dretay/stm32l051c8t_pulsar_p2/pics/IMG_5699.jpg

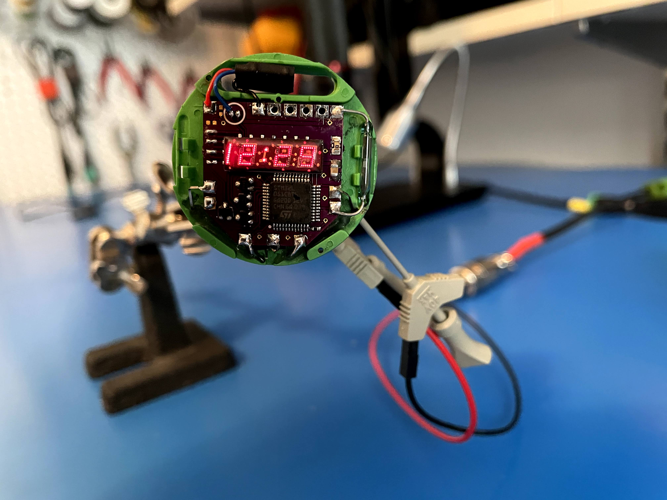
pics/IMG_5699.jpg
